0xJeremy/Dum-E-IOT/images/image2.jpeg

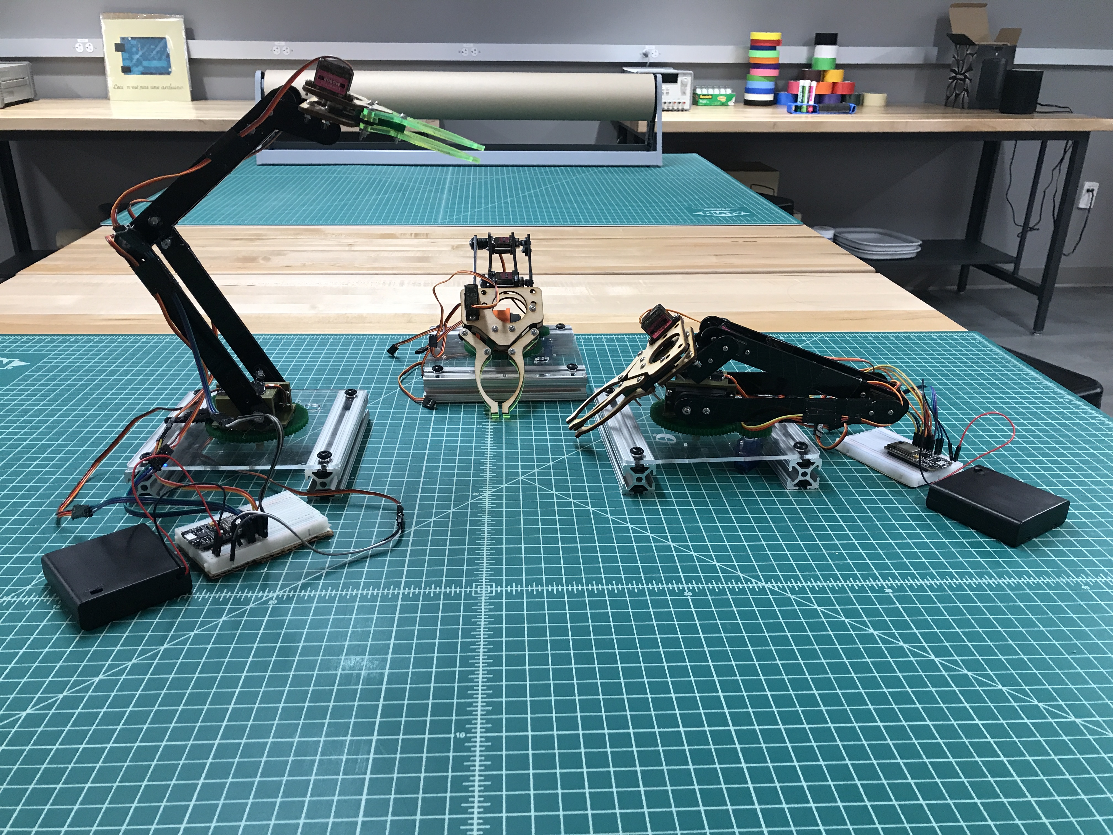
images/image2.jpeg
