0xJeremy/Dum-E-IOT/Robot Files/Base Files/BaseplateTop3.dxf

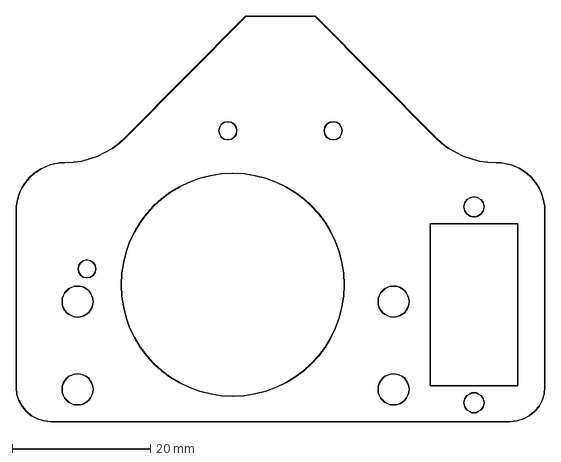
[picture p20: CAD file, 2019-03-09]
Robot Files/Base Files/BaseplateTop3.dxf
76.5 x 58.6 mm
