0xJeremy/Dum-E-IOT/Robot Files/Base Files/3in-72tooth-gear-with-quarter-inch-hole.SLDPRT

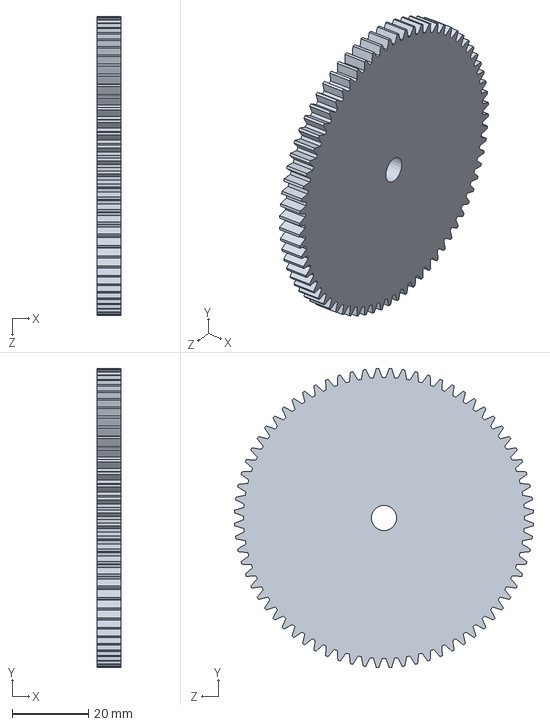
[picture p21: CAD file, 2019-03-09]
Robot Files/Base Files/3in-72tooth-gear-with-quarter-inch-hole.SLDPRT
6.35 x 78.3 x 78.3 mm
