0xJeremy/Dum-E-IOT/images/image3.jpeg

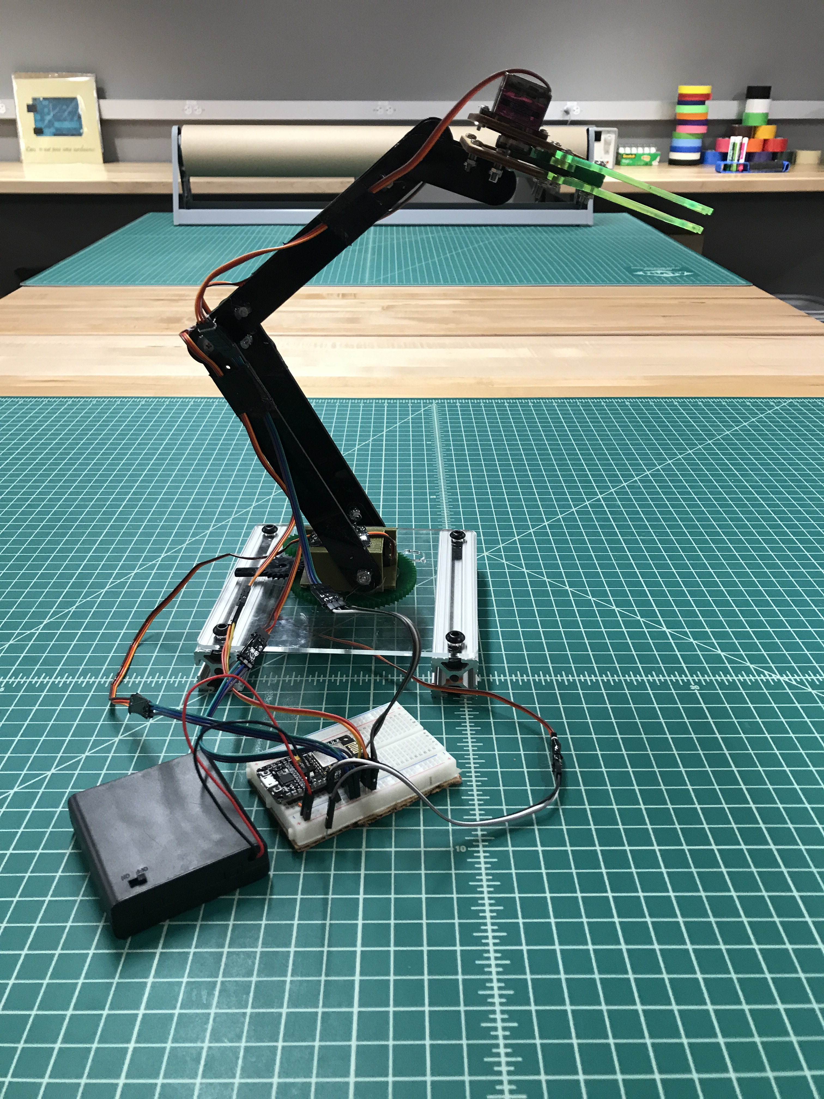
images/image3.jpeg
