0xJeremy/Dum-E-IOT/images/image4.jpeg

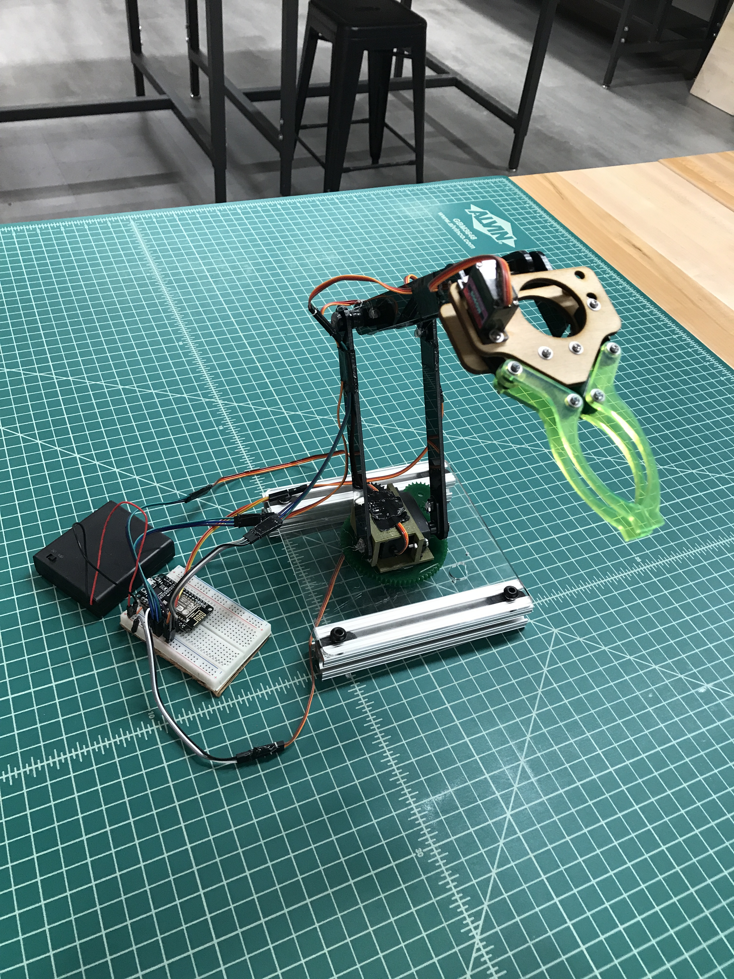
images/image4.jpeg
