0xJeremy/Dum-E-IOT/images/image5.jpeg

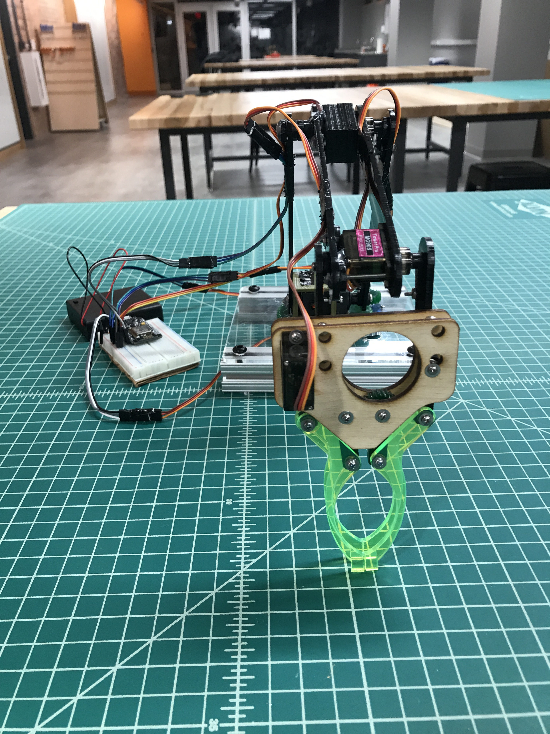
images/image5.jpeg
